promesoft/KicadJE_3340_Experiment/KicadJE_AS3340_RevA_Faceplate.jpg

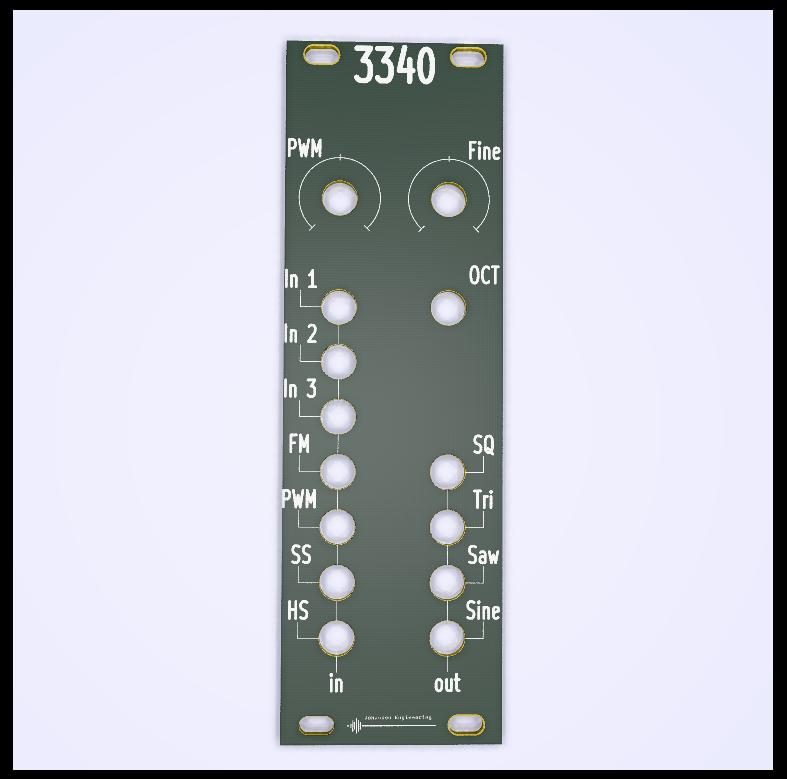
KicadJE_AS3340_RevA_Faceplate.jpg
